LukedeMunk/holoclock_v2/hardware/3D models/needle_minute.stl

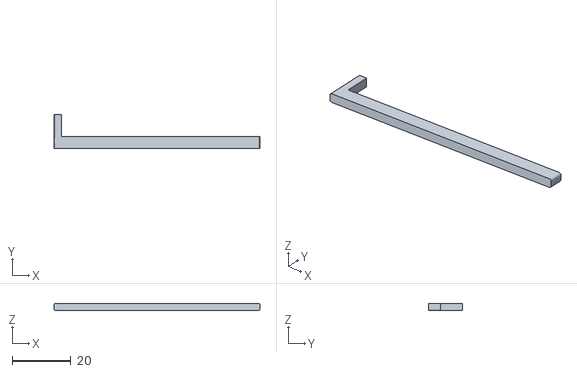
[picture p17: CAD file, 2022-03-11]
hardware/3D models/needle_minute.stl
70.0 x 11.5 x 2.50
