LukedeMunk/holoclock_v2/hardware/3D models/wheel_2.stl

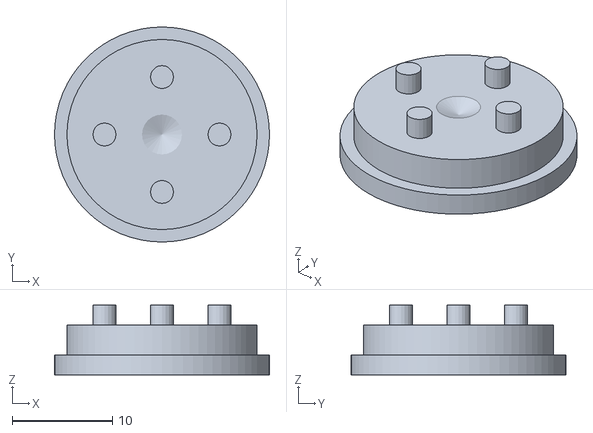
[picture p18: CAD file, 2022-03-11]
hardware/3D models/wheel_2.stl
21.5 x 21.5 x 6.99
