LukedeMunk/holoclock_v2/hardware/3D models/needle_hour.stl

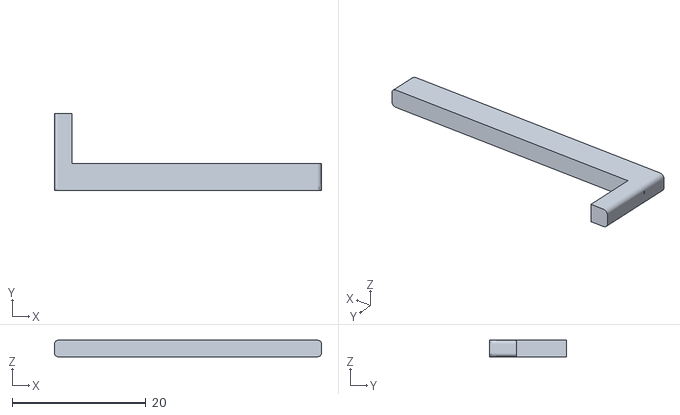
[picture p19: CAD file, 2022-03-11]
hardware/3D models/needle_hour.stl
40.0 x 11.5 x 2.50
