LukedeMunk/holoclock_v2/hardware/3D models/joiner_10mm.stl

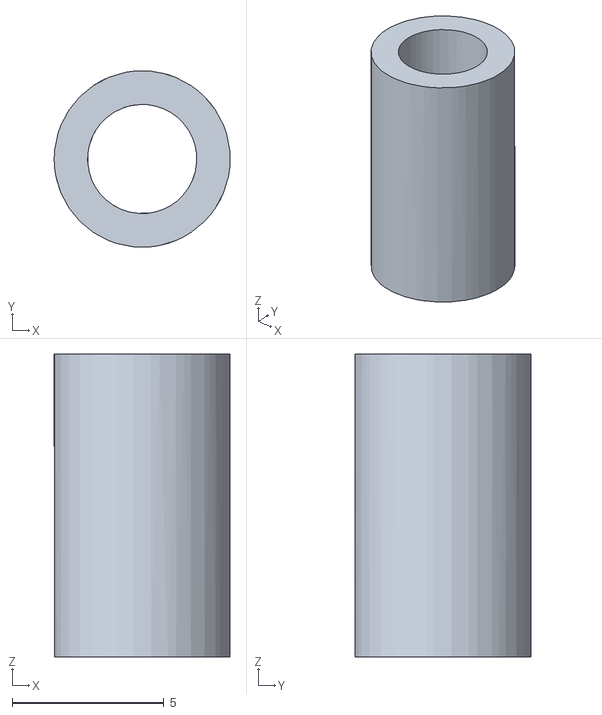
[picture p20: CAD file, 2022-03-11]
hardware/3D models/joiner_10mm.stl
5.80 x 5.80 x 10.0
