LukedeMunk/holoclock_v2/hardware/3D models/roller_stopper.stl

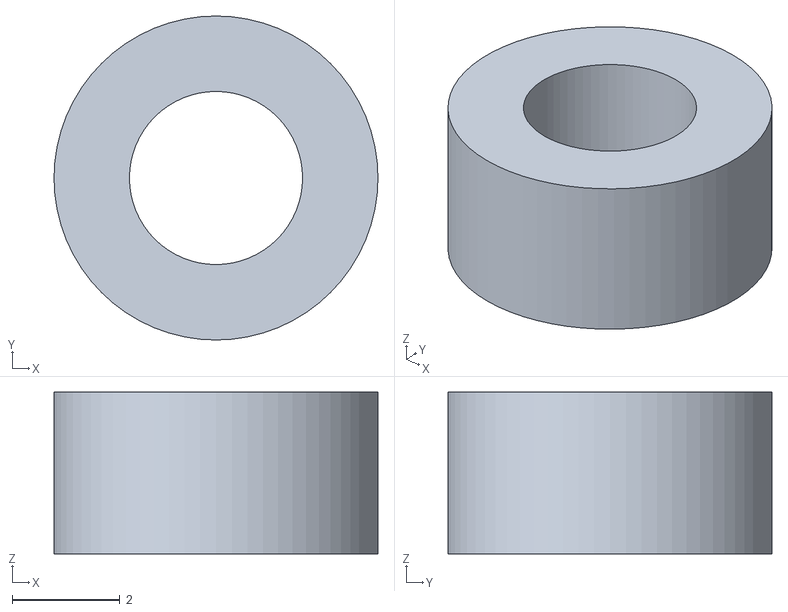
[picture p21: CAD file, 2022-03-11]
hardware/3D models/roller_stopper.stl
6.00 x 6.00 x 3.00
