LukedeMunk/holoclock_v2/hardware/3D models/spacer_10mm.stl

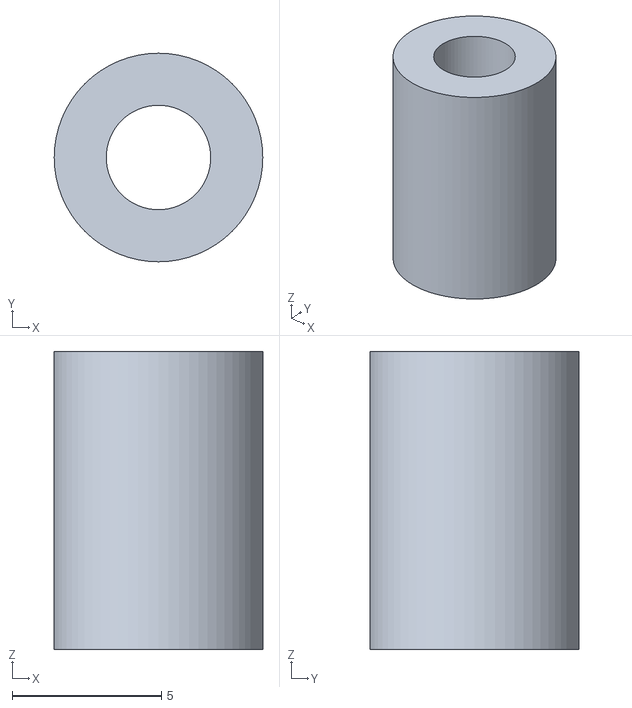
[picture p22: CAD file, 2022-03-11]
hardware/3D models/spacer_10mm.stl
7.00 x 7.00 x 10.0
