LukedeMunk/holoclock_v2/hardware/3D models/spacer_14mm.stl

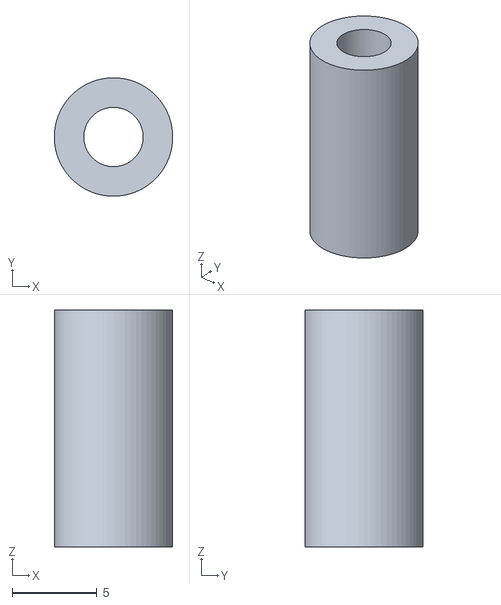
[picture p23: CAD file, 2022-03-11]
hardware/3D models/spacer_14mm.stl
7.00 x 7.00 x 14.0
