LukedeMunk/holoclock_v2/hardware/3D models/base_2.stl

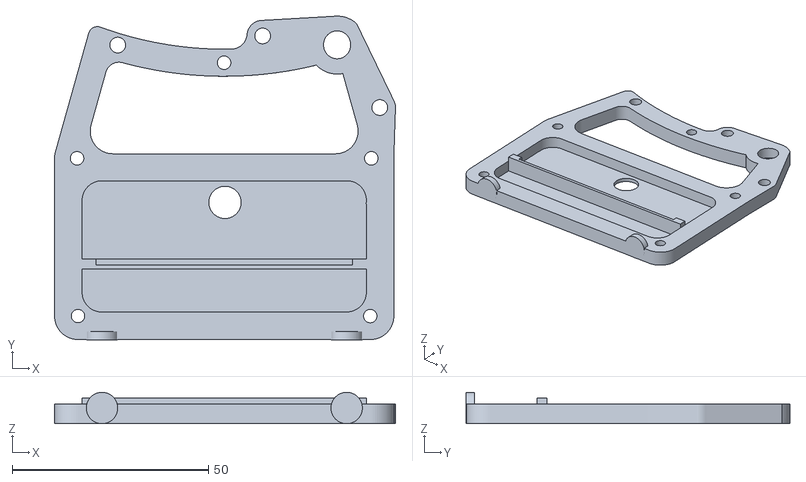
[picture p24: CAD file, 2022-03-11]
hardware/3D models/base_2.stl
86.8 x 82.4 x 8.00
