LukedeMunk/holoclock_v2/hardware/3D models/frame_l.stl

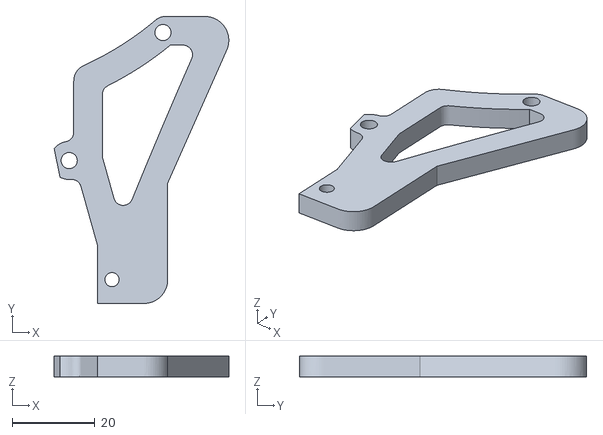
[picture p25: CAD file, 2022-03-11]
hardware/3D models/frame_l.stl
42.1 x 69.2 x 5.00
