LukedeMunk/holoclock_v2/hardware/3D models/big_ring.stl

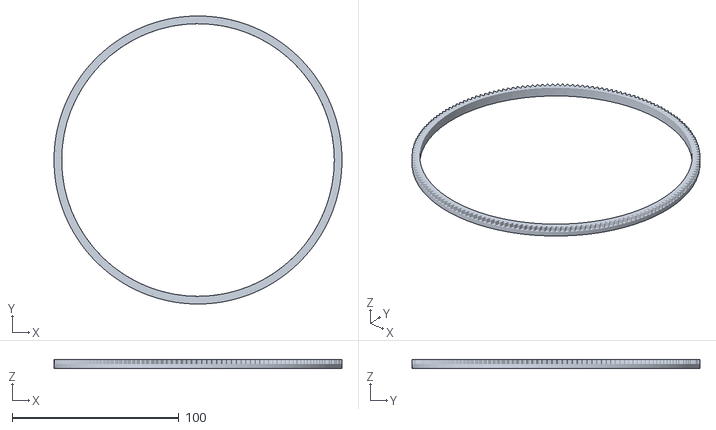
[picture p26: CAD file, 2022-03-11]
hardware/3D models/big_ring.stl
172.5 x 172.5 x 5.60
